page-tek/GNSS_Firehose/kicad/firehose_01_ch1.sch

## KiCad design kicad/firehose_01_ch1.sch (2018-09-16)

Schematic: firehose_01_ch1.sch

Parts:
C1, C10, C11, C12, C13, C14: 47nF; 0402
C5: 10nF; 0402
C6, C7, C8, C9, C17, C27, C207: 100pF; 0402
C15: 2.2nF; 0402
C16: 33nF; 0402
C18, C19, C28, C29, C30, C31, C32, C33, C34, C35, C36, C37, C242, C243: 100n; 0402
C20, C21, C22, C23, C24, C25, C26: 1000pF; 0402
C208: 100nF; 0402
C209: 10uF; 0805
FB11, FB14: 240; 0603
J1: SMA; SMA_END_LAUNCH
L2: 6 nH; 0402
L12: 47 nH; 0402
R1: 86.6; 0402
R3: 43.2; 0402
R4: 820; 0402
R5: 390; 0402
R6, R79, R80: 10k; 0402
R7: 80; 0402
R8: 33; 0402
R126: 0; 0603
RN6, RN7: 33; 1206_4R
U1: MAX2112; QFN28_EP
U2: MAX19505; QFN48_EP
U3: BGA2800; SOT-363
U20: MIC2090-1YM5; SOT-23-5

Notes on the sheet:
antenna power bias tee
LNA
downconverter
ADC
loop filter
RF channel 1
