page-tek/GNSS_Firehose/kicad/firehose_02_ch2.sch

## KiCad design kicad/firehose_02_ch2.sch (2018-09-16)

Schematic: firehose_02_ch2.sch

Parts:
C67, C73, C74, C75, C76, C77: 47nF; 0402
C68: 10nF; 0402
C69, C70, C71, C72, C80, C90, C210: 100pF; 0402
C78: 2.2nF; 0402
C79: 33nF; 0402
C81, C82, C91, C92, C93, C94, C95, C96, C97, C98, C99, C100, C211, C244, C245: 100n; 0402
C83, C84, C85, C86, C87, C88, C89: 1000pF; 0402
C212: 10uF; 0805
FB12, FB15: 240; 0603
J2: SMA; SMA_END_LAUNCH
L4: 6 nH; 0402
L13: 47 nH; 0402
R12: 33; 0402
R17: 86.6; 0402
R19: 43.2; 0402
R20: 820; 0402
R21: 390; 0402
R22, R81, R82: 10k; 0402
R23: 80; 0402
R127: 0; 0603
RN8, RN9: 33; 1206_4R
U4: MAX2112; QFN28_EP
U5: MAX19505; QFN48_EP
U6: BGA2800; SOT-363
U21: MIC2090-1YM5; SOT-23-5

Notes on the sheet:
antenna power bias tee
LNA
downconverter
ADC
loop filter
RF channel 2
