page-tek/GNSS_Firehose/kicad/firehose_03_ch3.sch

## KiCad design kicad/firehose_03_ch3.sch (2018-09-16)

Schematic: firehose_03_ch3.sch

Parts:
C102, C108, C109, C110, C111, C112: 47nF; 0402
C103: 10nF; 0402
C104, C105, C106, C107, C115, C125, C213: 100pF; 0402
C113: 2.2nF; 0402
C114: 33nF; 0402
C116, C117, C126, C127, C128, C129, C130, C131, C132, C133, C134, C135, C237, C246, C247: 100n; 0402
C118, C119, C120, C121, C122, C123, C124: 1000pF; 0402
C254: 10uF; 0805
FB13, FB16: 240; 0603
J3: SMA; SMA_END_LAUNCH
L6: 6 nH; 0402
L14: 47 nH; 0402
R14: 33; 0402
R25: 86.6; 0402
R27: 43.2; 0402
R28: 820; 0402
R29: 390; 0402
R30, R83, R84: 10k; 0402
R31: 80; 0402
R128: 0; 0603
RN10, RN11: 33; 1206_4R
U7: MAX2112; QFN28_EP
U8: MAX19505; QFN48_EP
U9: BGA2800; SOT-363
U22: MIC2090-1YM5; SOT-23-5

Notes on the sheet:
antenna power bias tee
LNA
downconverter
ADC
loop filter
RF channel 3
