page-tek/GNSS_Firehose/kicad/firehose_04_ch4.sch

## KiCad design kicad/firehose_04_ch4.sch (2018-09-16)

Schematic: firehose_04_ch4.sch

Parts:
C41, C42, C43, C137, C138, C139, C140, C201, C202, C203, C204, C205, C206: 100n; 0402
C156, C238, C239, C240, C241: DNF; 0402
J4, J5: SMA; SMA_END_LAUNCH
L20, L21: 0; 0603
R16: 33; 0402
R33, R37: 49.9; 0402
R34, R35: 60.4; 0402
R36: 249; 0402
R129, R130: DNF; 0402
R131, R135, R136: 0; 0402
RN12, RN13: 33; 1206_4R
U10: MAX19505; QFN48_EP

Notes on the sheet:
ADC
optional LPF
optional pad
optional AC coupling
