page-tek/GNSS_Firehose/kicad/firehose_05_clock.sch

## KiCad design kicad/firehose_05_clock.sch (2018-09-16)

Schematic: firehose_05_clock.sch

Parts:
C44, C45, C46, C47, C49, C51, C54, C55, C56, C57, C58, C59, C60, C61, C62, C63, C64, C65, C66, C229, C230: 100n; 0402
C53: 10uF; 0805
C214: 220pF; 0402
C215: 18nF; 0603
C231, C232, C233, C234, C235, C236, C255: 10pF; 0402
C256: DNF; 0402
FB4, FB5, FB6, FB7, FB8, FB9, FB10: 240; 0402
L15, L17, L19: 56 nH; 0603
OSC1: TCXO; D75J
R9: 150; 0402
R10: 220; 0402
R11, R13, R15: 80; 0402
R88: 820; 0402
R132: 0; 0402
TP3, TP4, TP11, TP12, TP16, TP17, TP27, TP28, TP29: test_point; TP_SMT
U15: LMK03806; LLP64_EP

Notes on the sheet:
38.88 MHz TCXO
clock synthesizer
