page-tek/GNSS_Firehose/kicad/firehose_06_fpga1.sch

## KiCad design kicad/firehose_06_fpga1.sch (2018-09-16)

Schematic: firehose_06_fpga1.sch

Parts:
C2, C3, C4, C38, C39, C40, C48, C50, C52, C101, C136, C141, C143, C144, C145, C146, C147, C149, C150, C151, C152, C153, C155, C157, C159, C160, C161, C163, C164, C165, C167, C168, C169, C170: 100n; 0402
C142, C148, C154, C158, C162, C166: 10uF; 0805
J6: HEADER_14; HEADER14_2MM
J9: HEADER_6; HEADER6_100MIL
LED1: LED; 0603
R2, R26: 1k; 0402
R18, R47: 4.7k; 0402
R42: 0; 0402
R45: 330; 0402
RN5: 33; 1206_4R
U11: AT25DF041A; SO8
U12: XS6SLX16FTG256; BGA256

Notes on the sheet:
JTAG
flash
VCCINT
VCCAUX
VCCO_0
VCCO_1
VCCO_2
VCCO_3
15p caps
