page-tek/GNSS_Firehose/kicad/firehose_07_fpga2.sch

## KiCad design kicad/firehose_07_fpga2.sch (2018-09-16)

Schematic: firehose_07_fpga2.sch

Parts:
C171, C172, C173, C248, C249, C257: 100n; 0402
J10: HEADER_16; HEADER16_100MIL
LED2, LED3: LED; APA2106
R24, R32, R85: 330; 0402
R38, R39, R40, R41, R53, R54, R58, R86: 1k; 0402
R43, R44, R46, R48, R49, R50, R55, R56, R57, R59: 10k; 0402
SW1: Push_SW; EVQP7
U12: XS6SLX16FTG256; BGA256
