page-tek/GNSS_Firehose/kicad/firehose_08_ethernet.sch

## KiCad design kicad/firehose_08_ethernet.sch (2018-09-16)

Schematic: firehose_08_ethernet.sch

Parts:
C176, C177: 33pF; 0402
C182, C183, C184, C185, C186, C187, C218, C219, C221, C222, C223, C224, C227, C228, C250, C251, C252, C253: 100n; 0402
C193, C216, C217, C220, C225, C226: 10uF; 0805
C258: NONE; 0603
FB1, FB2, FB3: 240; 0603
J7: L829-1J1T-43
R51, R52: 220; 0402
R60: NONE; 0603
R95: 12.1k 1%; 0402
R96: 470; 0402
R97, R116, R117, R124: 10k; 0402
R98, R99: 0; 0603
R106, R109, R110, R113, R118, R119, R123: 1k; 0402
R107: 4.7k; 0402
R108, R111, R112, R114, R115, R120, R121, R122, R125: NONE; 0402
RN1, RN2, RN3, RN4: 33; 1206_4R
TP22: test_point; TP_SMT
U18: KSZ9031RNX; QFN48_EP_MICREL
Y1: 25 MHz; CTS_ATS

Notes on the sheet:
Ethernet
