page-tek/GNSS_Firehose/kicad/firehose_09_power.sch

## KiCad design kicad/firehose_09_power.sch (2018-09-16)

Schematic: firehose_09_power.sch

Parts:
C174: 100nF; 0402
C175, C178, C179, C189, C190, C191, C192, C194, C195, C196, C197, C198, C199, C200: 10uF; 0805
C180, C181, C188: C; 0402
FB18, FB19: L; 0603
J8: PJ-063BH
LED4: LED; APA2106
Q1: Si2369DS; SOT23
R61, R62, R63, R64, R65, R66: R; 0402
R67, R68, R69: 0; 0402
R75: 330; 0402
TP1, TP5: 1V2; TP_SMT2MM
TP2, TP6: 3V3_DIG; TP_SMT2MM
TP7, TP8: 3V3_AN; TP_SMT2MM
TP21, TP23, TP24: test_point; TP_SMT
U13, U14, U16: LMZ10501; LDFN8
Z1: SMAJ9.0CA; SMAJ

Notes on the sheet:
Power
DC input
