page-tek/GNSS_Firehose/kicad/firehose_10_mechanical.sch

## KiCad design kicad/firehose_10_mechanical.sch (2018-09-16)

Schematic: firehose_10_mechanical.sch

Parts:
FID1, FID2, FID3: fiducial; FIDUCIAL
MH1, MH2, MH3, MH4: mounting_hole; HOLE_UNC_2_56
SC1, SC2, SC3, SC4, SC5, SC6, SC7, SC8: shield_clip; S1721

Notes on the sheet:
mounting holes
shield clips for RF channels
fiducials
Mechanical
