page-tek/GNSS_Firehose/fpga/hdl/quantize.v

// Simple 2-bit quantizer
// to be replaced with an AGC scheme later
//
// GNSS Firehose
// Copyright (c) 2012 Peter Monta <pmonta@gmail.com>

module quantize(
  input clk,
  input [7:0] x,
  input [7:0] offset,
  input [9:0] random,
  output reg [1:0] y
);

  wire [17:0] t = {x,random};
  wire [17:0] t2 = t + {{5{offset[7]}},offset,5'd0};

  always @(posedge clk)
    casex (t2)
      18'b00000xxxxxxxxxxxxx: y <= 2'b00; //was 10
      18'b11111xxxxxxxxxxxxx: y <= 2'b11; //was 01
      18'b0xxxxxxxxxxxxxxxxx: y <= 2'b01; //was 11
      default:                y <= 2'b10; //was 00
    endcase

endmodule
